edouardprudhomme/AM-Radio-Receiver/Hardware/Radio.kicad_sch

## KiCad design Hardware/Radio.kicad_sch (2026-07-02)

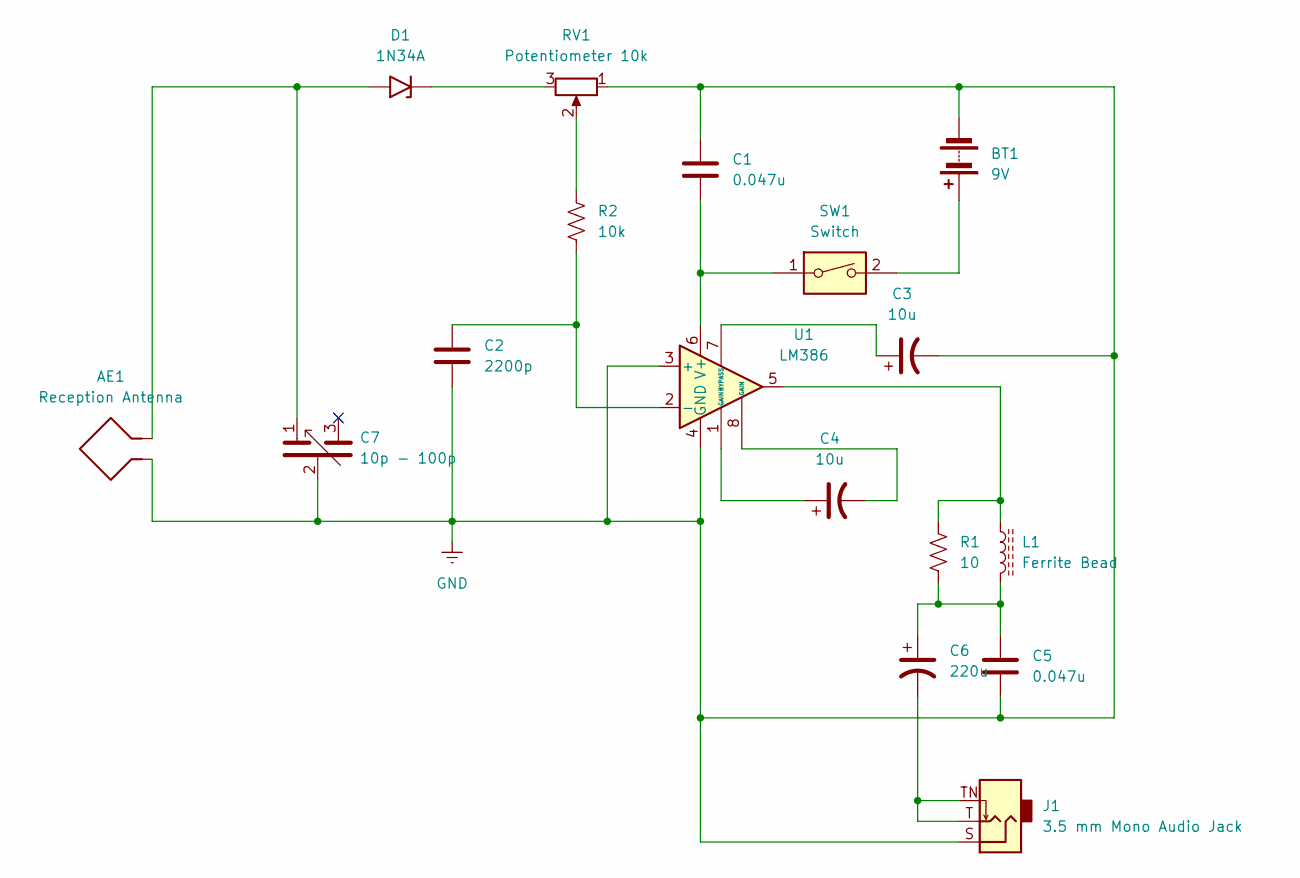
[picture p2: schematic Radio.kicad_sch]

Parts:
AE1: Reception Antenna
BT1: 9V
C1, C5: 0.047u
C2: 2200p
C3, C4: 10u
C6: 220u
C7: 10p - 100p
D1: 1N34A; D_DO-201AE_P15.24mm_Horizontal
J1: 3.5 mm Mono Audio Jack
L1: Ferrite Bead
R1: 10
R2: 10k
RV1: Potentiometer 10k
SW1: Switch
U1: LM386

Connections:
GND: AE1.1, BT1.2 (-), C1.1, C2.2, C3.2, C5.2, C7.2, J1.S, RV1.1, U1.3 (+), U1.4 (GND)
unnamed: AE1.2, C7.1, D1.2 (A2)
unnamed: BT1.1 (+), SW1.2
unnamed: C1.2, SW1.1, U1.6 (V+)
unnamed: C2.1, R2.2, U1.2 (-)
unnamed: C3.1, U1.7 (BYPASS)
unnamed: C4.1, U1.1 (GAIN)
unnamed: C4.2, U1.8 (GAIN)
unnamed: C5.1, C6.1, L1.2, R1.1
unnamed: C6.2, J1.T, J1.TN
unnamed: D1.1 (A1), RV1.3
unnamed: L1.1, R1.2, U1.5
unnamed: R2.1, RV1.2
